maxadler1979/palmira/foto/kb_top.png

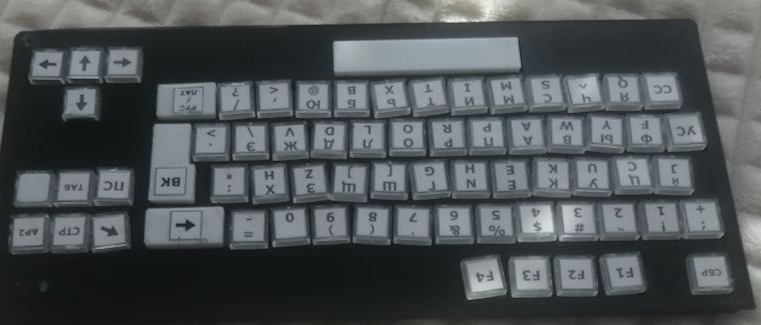
foto/kb_top.png
