maxadler1979/palmira/games/trex/splash.h

unsigned char zastavka[2050] = {32,64,
	
	0x17, 0x17, 0x17, 0x17, 0x17, 0x17, 0x17, 0x17, 0x17, 0x17, 0x17, 0x17, 0x17, 0x17, 0x17, 0x17, 
	0x17, 0x17, 0x17, 0x17, 0x17, 0x17, 0x17, 0x17, 0x17, 0x17, 0x17, 0x17, 0x17, 0x17, 0x17, 0x13, 
	0x03, 0x03, 0x17, 0x17, 0x17, 0x17, 0x17, 0x17, 0x17, 0x17, 0x17, 0x17, 0x17, 0x17, 0x17, 0x17, 
	0x17, 0x17, 0x17, 0x17, 0x17, 0x17, 0x17, 0x17, 0x17, 0x13, 0x17, 0x17, 0x17, 0x17, 0x17, 0x17, 
	0x17, 0x17, 0x17, 0x17, 0x17, 0x17, 0x17, 0x17, 0x17, 0x17, 0x17, 0x17, 0x13, 0x02, 0x17, 0x17, 
	0x17, 0x17, 0x17, 0x17, 0x17, 0x17, 0x17, 0x17, 0x17, 0x17, 0x17, 0x17, 0x17, 0x03, 0x00, 0x00, 
	0x00, 0x00, 0x02, 0x07, 0x17, 0x17, 0x17, 0x17, 0x17, 0x17, 0x17, 0x17, 0x17, 0x17, 0x17, 0x17, 
	0x17, 0x17, 0x17, 0x17, 0x17, 0x17, 0x17, 0x17, 0x17, 0x11, 0x02, 0x17, 0x17, 0x17, 0x17, 0x17, 
	0x17, 0x17, 0x17, 0x17, 0x17, 0x17, 0x03, 0x03, 0x17, 0x17, 0x17, 0x17, 0x00, 0x00, 0x06, 0x17, 
	0x17, 0x17, 0x17, 0x17, 0x13, 0x03, 0x17, 0x17, 0x17, 0x17, 0x13, 0x03, 0x00, 0x00, 0x00, 0x00, 
	0x00, 0x00, 0x00, 0x00, 0x06, 0x17, 0x17, 0x17, 0x17, 0x17, 0x17, 0x17, 0x03, 0x03, 0x01, 0x00, 
	0x06, 0x17, 0x17, 0x17, 0x17, 0x17, 0x17, 0x13, 0x00, 0x17, 0x00, 0x02, 0x17, 0x17, 0x17, 0x17, 
	0x17, 0x17, 0x17, 0x17, 0x17, 0x00, 0x00, 0x00, 0x00, 0x00, 0x01, 0x00, 0x00, 0x00, 0x00, 0x17, 
	0x17, 0x17, 0x17, 0x01, 0x00, 0x00, 0x17, 0x13, 0x03, 0x00, 0x00, 0x00, 0x00, 0x00, 0x00, 0x00, 
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
	0x14, 0x17, 0x15, 0x17, 0x15, 0x14, 0x14, 0x14, 0x14, 0x14, 0x14, 0x14, 0x14, 0x14, 0x14, 0x14, 
	0x14, 0x14, 0x14, 0x14, 0x14, 0x14, 0x14, 0x16, 0x00, 0x05, 0x05, 0x05, 0x05, 0x05, 0x05, 0x05, 
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
};
