maxadler1979/palmira/games/2048/img.h

#ifndef IMG_H
#define IMG_H


// n1.bmp / 16x12
  unsigned char bitmapN1[] = {

	0x13, 0x03, 0x03, 0x03, 0x03, 0x07, 0x00, 0x00,
        0x11, 0x00, 0x14, 0x17, 0x00, 0x06, 0x00, 0x00, 
	0x11, 0x00, 0x03, 0x17, 0x00, 0x06, 0x00, 0x00,
        0x11, 0x00, 0x00, 0x17, 0x00, 0x06, 0x00, 0x00, 
	0x11, 0x06, 0x17, 0x17, 0x17, 0x06, 0x00, 0x00,
        0x15, 0x14, 0x14, 0x14, 0x14, 0x16, 0x00, 0x00
};

// n2.bmp / 16x12
  unsigned char bitmapN2[] = {

	0x13, 0x03, 0x03, 0x03, 0x03, 0x07, 0x00, 0x00, 0x11, 0x04, 0x17, 0x17, 0x15, 0x06, 0x00, 0x00, 
	0x11, 0x06, 0x11, 0x04, 0x17, 0x06, 0x00, 0x00, 0x11, 0x00, 0x16, 0x13, 0x01, 0x06, 0x00, 0x00, 
	0x11, 0x06, 0x17, 0x17, 0x17, 0x06, 0x00, 0x00, 0x15, 0x14, 0x14, 0x14, 0x14, 0x16, 0x00, 0x00
};

// n3.bmp / 16x12
  unsigned char bitmapN3[] = {

	0x13, 0x03, 0x03, 0x03, 0x03, 0x07, 0x00, 0x00, 0x11, 0x06, 0x17, 0x17, 0x15, 0x06, 0x00, 0x00, 
	0x11, 0x00, 0x14, 0x14, 0x17, 0x06, 0x00, 0x00, 0x11, 0x00, 0x03, 0x03, 0x17, 0x06, 0x00, 0x00, 
	0x11, 0x06, 0x17, 0x17, 0x13, 0x06, 0x00, 0x00, 0x15, 0x14, 0x14, 0x14, 0x14, 0x16, 0x00, 0x00
};

// n4.bmp / 16x12
  unsigned char bitmapN4[] = {

	0x13, 0x03, 0x03, 0x03, 0x03, 0x07, 0x00, 0x00, 0x11, 0x00, 0x00, 0x16, 0x11, 0x06, 0x00, 0x00, 
	0x11, 0x00, 0x16, 0x07, 0x11, 0x06, 0x00, 0x00, 0x11, 0x06, 0x15, 0x16, 0x15, 0x06, 0x00, 0x00, 
	0x11, 0x00, 0x03, 0x07, 0x13, 0x06, 0x00, 0x00, 0x15, 0x14, 0x14, 0x14, 0x14, 0x16, 0x00, 0x00
};

// n5.bmp / 16x12
  unsigned char bitmapN5[] = {

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
 
	0x00, 0x00, 0x00, 0x00, 0x00, 0x00, 0x00, 0x00, 0x00, 0x13, 0x03, 0x03, 0x07, 0x00, 0x00, 0x00, 
	0x00, 0x11, 0x03, 0x13, 0x06, 0x00, 0x00, 0x00, 0x00, 0x11, 0x16, 0x14, 0x06, 0x00, 0x00, 0x00, 
	0x00, 0x15, 0x14, 0x14, 0x16, 0x00, 0x00, 0x00, 0x00, 0x00, 0x00, 0x00, 0x00, 0x00, 0x00, 0x00
};

// s2_6.bmp / 16x12
unsigned char bitmapS2_6[] = {
 
	0x04, 0x14, 0x14, 0x14, 0x14, 0x10, 0x00, 0x00, 0x06, 0x00, 0x14, 0x14, 0x00, 0x11, 0x00, 0x00, 
	0x06, 0x06, 0x13, 0x07, 0x11, 0x11, 0x00, 0x00, 0x06, 0x00, 0x16, 0x03, 0x00, 0x11, 0x00, 0x00, 
	0x06, 0x02, 0x03, 0x03, 0x01, 0x11, 0x00, 0x00, 0x02, 0x03, 0x03, 0x03, 0x03, 0x01, 0x00, 0x00
};

unsigned char Empty_sprite[] = {
 
	0x00, 0x00, 0x00, 0x00, 0x00, 0x00, 0x00, 0x00, 0x00, 0x00, 0x00, 0x00, 0x00, 0x00, 0x00, 0x00, 
	0x00, 0x00, 0x00, 0x00, 0x00, 0x00, 0x00, 0x00, 0x00, 0x00, 0x00, 0x00, 0x00, 0x00, 0x00, 0x00, 
	0x00, 0x00, 0x00, 0x00, 0x00, 0x00, 0x00, 0x00, 0x00, 0x00, 0x00, 0x00, 0x00, 0x00, 0x00, 0x00
};

#endif
