maxadler1979/palmira/games/trex/dino.h

#ifndef __DINO_H
#define __DINO_H




unsigned char dino_duck1[100] = {7,14,
	0x04, 0x00, 0x00, 0x00, 0x00, 0x00, 0x00, 0x00, 0x00, 0x04, 0x14, 0x14, 0x14, 0x10, 0x06, 0x17, 
	0x14, 0x14, 0x17, 0x17, 0x17, 0x17, 0x14, 0x17, 0x07, 0x17, 0x17, 0x17, 0x00, 0x07, 0x17, 0x17, 
	0x17, 0x17, 0x17, 0x17, 0x17, 0x17, 0x17, 0x17, 0x17, 0x17, 0x00, 0x00, 0x07, 0x17, 0x17, 0x17, 
	0x17, 0x17, 0x17, 0x17, 0x17, 0x13, 0x03, 0x03, 0x00, 0x00, 0x00, 0x07, 0x17, 0x17, 0x13, 0x07, 
	0x01, 0x02, 0x03, 0x03, 0x03, 0x00, 0x00, 0x00, 0x00, 0x15, 0x06, 0x13, 0x00, 0x02, 0x01, 0x00, 
	0x00, 0x00, 0x00, 0x00, 0x00, 0x00, 0x00, 0x00, 0x06, 0x10, 0x00, 0x00, 0x00, 0x00, 0x00, 0x00, 
	0x00, 0x00
};
unsigned char dino_duck2[100] = {7,14,
	0x04, 0x00, 0x00, 0x00, 0x00, 0x00, 0x00, 0x00, 0x00, 0x04, 0x14, 0x14, 0x14, 0x10, 0x06, 0x17, 
	0x14, 0x14, 0x17, 0x17, 0x17, 0x17, 0x14, 0x17, 0x07, 0x17, 0x17, 0x17, 0x00, 0x07, 0x17, 0x17, 
	0x17, 0x17, 0x17, 0x17, 0x17, 0x17, 0x17, 0x17, 0x17, 0x17, 0x00, 0x00, 0x07, 0x17, 0x17, 0x17, 
	0x17, 0x17, 0x17, 0x17, 0x17, 0x13, 0x03, 0x03, 0x00, 0x00, 0x00, 0x07, 0x17, 0x17, 0x13, 0x07, 
	0x01, 0x02, 0x03, 0x03, 0x03, 0x00, 0x00, 0x00, 0x00, 0x17, 0x01, 0x02, 0x03, 0x02, 0x01, 0x00, 
	0x00, 0x00, 0x00, 0x00, 0x00, 0x00, 0x00, 0x15, 0x00, 0x00, 0x00, 0x00, 0x00, 0x00, 0x00, 0x00, 
	0x00, 0x00

};
unsigned char dino_duck3[100] = {7,14,
	0x00, 0x00, 0x00, 0x00, 0x00, 0x00, 0x00, 0x00, 0x00, 0x0, 0x0, 0x0, 0x0, 0x0, 0x0, 0x0, 
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
unsigned char         x; 
unsigned char         **dino_ptr;                     // выбор спрайтов 
unsigned char         AnimFrame;                    // номер выводимого спрайта
unsigned char         AnimFrame_delay;                    // номер выводимого спрайта

}dino_t;

#endif 
