maxadler1979/palmira/games/trex/cactus.h

unsigned char cactus_big_big[130] = { //13x10
	
	0x00, 0x00, 0x00, 0x16, 0x17, 0x17, 0x17, 0x02, 0x00, 0x00,
        0x00, 0x00, 0x00, 0x10, 0x11, 0x11, 0x15, 0x17, 0x00, 0x14,
        0x16, 0x17, 0x17, 0x17, 0x17, 0x17, 0x17, 0x17, 0x17, 0x17,
        0x10, 0x11, 0x11, 0x11, 0x11, 0x11, 0x15, 0x13, 0x11, 0x15,
        0x00, 0x00, 0x04, 0x17, 0x17, 0x17, 0x17, 0x01,	0x00, 0x10,
        0x00, 0x00, 0x00, 0x11, 0x11, 0x11, 0x01, 0x00, 0x00, 0x00,
        0x00, 0x00, 0x04, 0x06, 0x06, 0x02, 0x00, 0x00, 0x00, 0x00,
        0x00, 0x10, 0x17, 0x17, 0x17, 0x07, 0x02, 0x00, 0x00, 0x04,
	0x04, 0x06, 0x06, 0x06, 0x06, 0x17, 0x07, 0x06, 0x06, 0x16,
        0x15, 0x17, 0x17, 0x17, 0x17, 0x17, 0x17, 0x17, 0x17, 0x17,
        0x00, 0x00, 0x00, 0x06, 0x06, 0x06, 0x17, 0x03, 0x00, 0x14,
        0x00, 0x00, 0x10, 0x17, 0x17, 0x17, 0x13, 0x00, 0x00, 0x00,
        0x00, 0x00, 0x00, 0x00, 0x00, 0x00, 0x00, 0x00, 0x00, 0x00
};



unsigned char cactus_big_small[110] = { // 11x10
	0x00, 0x00, 0x00, 0x04, 0x06, 0x06, 0x06, 0x00, 0x00, 0x00,
        0x00, 0x00, 0x00, 0x15, 0x17, 0x17, 0x17, 0x07, 0x00, 0x04,
        0x04, 0x06, 0x06, 0x06, 0x06, 0x06, 0x16, 0x17, 0x06, 0x16,
        0x15, 0x17, 0x17, 0x17, 0x17, 0x17, 0x17, 0x17, 0x17, 0x17,
        0x00, 0x00, 0x00, 0x06, 0x06, 0x06, 0x16, 0x03, 0x00, 0x14,
        0x00, 0x00, 0x10, 0x17, 0x17, 0x17, 0x13, 0x00, 0x00, 0x00,
        0x00, 0x00, 0x00, 0x00, 0x06, 0x06, 0x06, 0x00, 0x00, 0x00,
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
unsigned char         speed;                        // Скорость в зависимости от уровня
unsigned char         x; 
unsigned char         *cactus_ptr;                     // выбор спрайтов 
unsigned char         AnimRow;                    // номер выводимого спрайта

}cactus_t;
