maxadler1979/palmira/games/trex/ptero.h

unsigned char ptero1[96] = {

	0x00, 0x04, 0x03, 0x00, 0x00, 0x00, 0x00, 0x00, 0x04, 0x17, 0x03, 0x00, 0x00, 0x00, 0x00, 0x00, 
	0x17, 0x17, 0x03, 0x00, 0x00, 0x00, 0x00, 0x00, 0x00, 0x11, 0x17, 0x02, 0x00, 0x00, 0x00, 0x00, 
	0x00, 0x00, 0x17, 0x17, 0x17, 0x17, 0x17, 0x01, 0x00, 0x00, 0x17, 0x17, 0x17, 0x13, 0x00, 0x00, 
	0x00, 0x00, 0x15, 0x17, 0x17, 0x00, 0x00, 0x00, 0x00, 0x00, 0x10, 0x17, 0x17, 0x00, 0x00, 0x00, 
	0x00, 0x00, 0x00, 0x13, 0x03, 0x00, 0x00, 0x00, 0x00, 0x00, 0x00, 0x03, 0x01, 0x00, 0x00, 0x00, 
	0x00, 0x00, 0x00, 0x00, 0x00, 0x00, 0x00, 0x00, 0x00, 0x00, 0x00, 0x00, 0x00, 0x00, 0x00, 0x00
};



unsigned char ptero2[96] = {

	0x00, 0x00, 0x00, 0x16, 0x00, 0x00, 0x00, 0x00,
        0x00, 0x00, 0x16, 0x17, 0x00, 0x00, 0x00, 0x00, 
	0x00, 0x14, 0x17, 0x17, 0x00, 0x00, 0x00, 0x00,
        0x06, 0x02, 0x10, 0x15, 0x07, 0x00, 0x00, 0x00, 
	0x10, 0x17, 0x17, 0x17, 0x17, 0x07, 0x00, 0x00, 
        0x00, 0x10, 0x17, 0x17, 0x17, 0x17, 0x03, 0x00, 
	0x00, 0x00, 0x10, 0x17, 0x17, 0x17, 0x03, 0x00, 
        0x00, 0x00, 0x00, 0x00, 0x15, 0x17, 0x03, 0x00, 
	0x00, 0x00, 0x00, 0x00, 0x14, 0x15, 0x00, 0x00, 
        0x00, 0x00, 0x00, 0x00, 0x14, 0x10, 0x00, 0x00, 
	0x00, 0x00, 0x00, 0x00, 0x00, 0x00, 0x00, 0x00, 
        0x00, 0x00, 0x00, 0x00, 0x00, 0x00, 0x00, 0x00
};
	

unsigned char *Ptero[] =
{
  ptero1,
  ptero2
};

typedef struct
{
    uint8_t    live;                      // Отображаем на экране?
   
    uint8_t    x;                            // координата по х
    uint8_t    y;                            // высота
    uint8_t    AnimFrame;                    // номер выводимого спрайта
    uint8_t    time_to_next_sprite;          // время до показа следующего спрайта
    unsigned char         *ptero_ptr;
    uint8_t    AnimRow
}pterodactyl_t;
