maxadler1979/palmira/games/2048/file_sys.c

extern void FS_Find(void);
extern void FS_Open(void);
extern void FS_Seek(void);
extern void FS_Read(void);
extern void FS_Write(void);

 int path;
 int max_files;

extern char* filename;
extern char mode;

 char fs_answer;
 char* adr;
 int bytes_loaded;
 int size;

 //char err_code;
 char mode;
 char* filename;
 int pointer;
 


 char from;
 char to;


 
