maxadler1979/palmira/games/2048/res.h

#ifndef RES_H
#define RES_H


#include "img.h"


unsigned char* ResPanelNormalList[] = {
	bitmapN1,
	bitmapN2,
	bitmapN3,
	bitmapN4,
	bitmapN5,
	bitmapN6,
	bitmapN7,
	bitmapN8,
	bitmapN9,
	bitmapNs,
};

unsigned char* ResPanelReverseList[] = {
	bitmapR1,
	bitmapR2,
	bitmapR3,
	bitmapR4,
	bitmapR5,
	bitmapR6,
	bitmapR7,
	bitmapR8,
	bitmapR9,
	bitmapRs,
};

unsigned char* ResPanelScale1List[] = {
	bitmapS1_1,
	bitmapS1_2,
	bitmapS1_3,
	bitmapS1_4,
	bitmapS1_5,
	bitmapS1_6,
	bitmapN1,
};

unsigned char* ResPanelScale2List[] = {
	bitmapS2_1,
	bitmapS2_2,
	bitmapS2_3,
	bitmapS2_4,
	bitmapS2_5,
	bitmapS2_6,
	bitmapN2,
};


#endif
